SteveRMann/Halloween-2023/dfPlayer/DFPlayer-Wemos-ESPHome.jpg

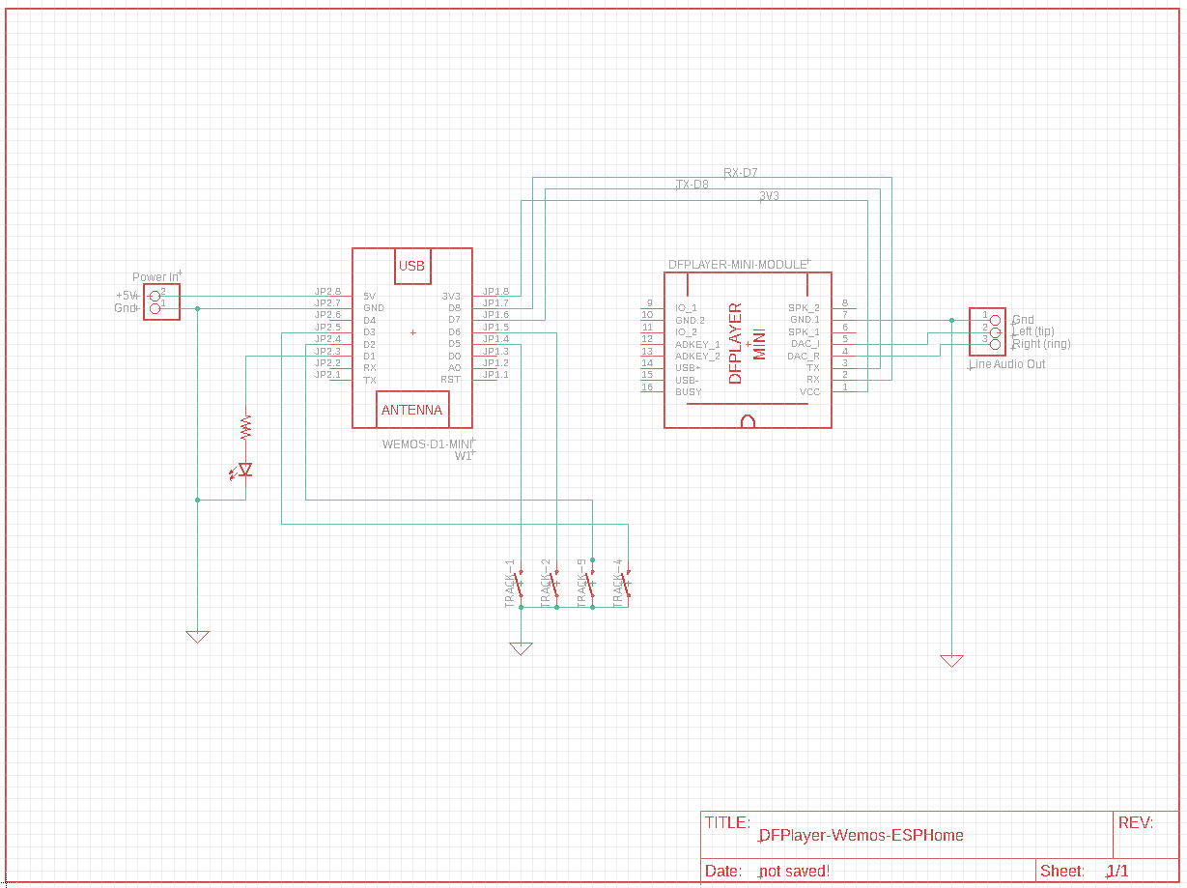
dfPlayer/DFPlayer-Wemos-ESPHome.jpg
