SteveRMann/Halloween-2023/dfPlayer/DFPlayer-Wemos-GPIO control.jpg

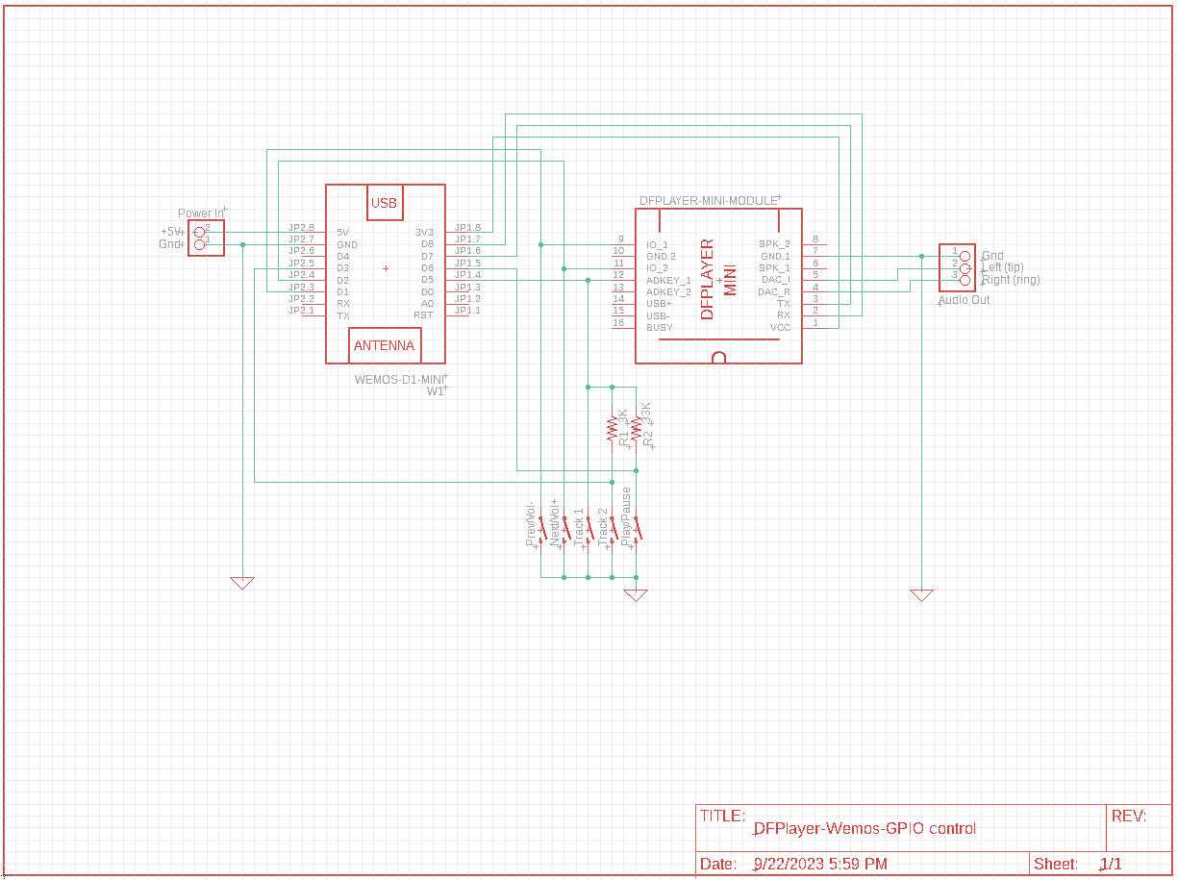
dfPlayer/DFPlayer-Wemos-GPIO control.jpg
