SteveRMann/Halloween-2023/dfPlayer/wemos_shield.png

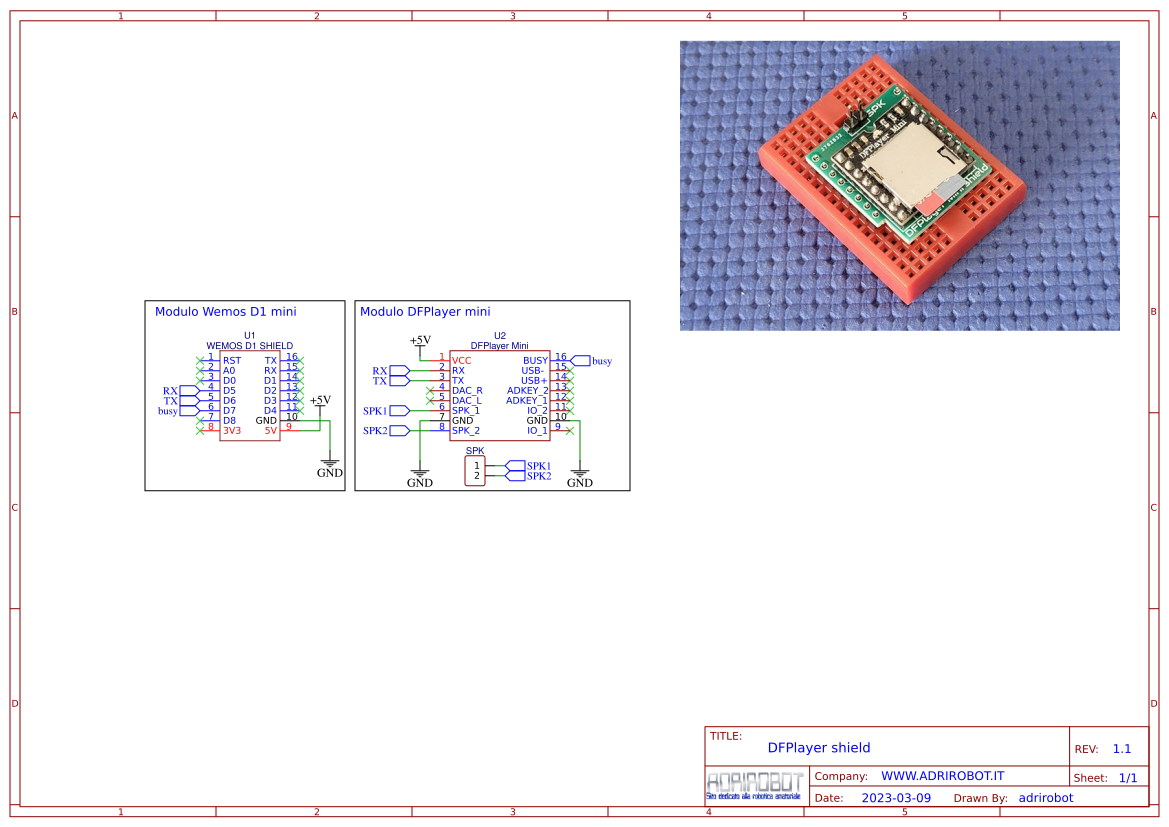
dfPlayer/wemos_shield.png
