SteveRMann/Halloween-2023/dfPlayer/DFPlayer-Wemos-ESPHome.sch

## EAGLE design dfPlayer/DFPlayer-Wemos-ESPHome.sch (2024-05-11)

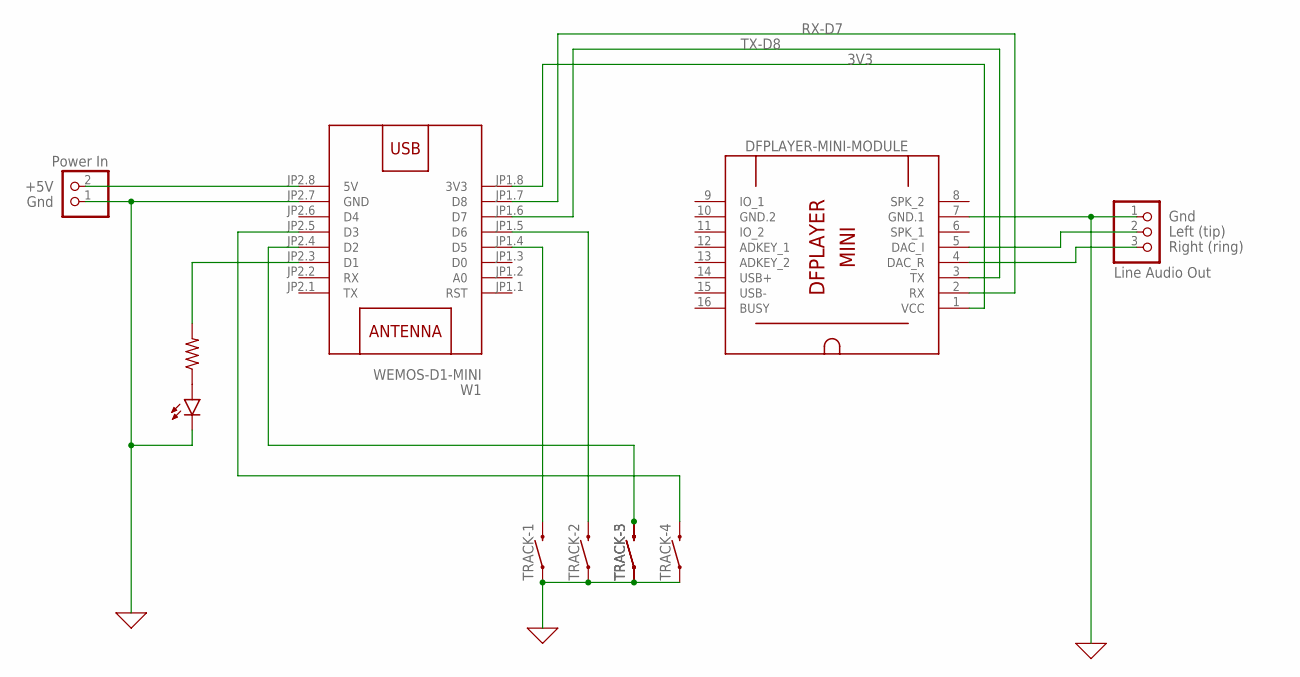
[picture p10: schematic DFPlayer-Wemos-ESPHome.sch]

Parts:
D1: WP7113SGD; RADIAL_5MM
JP2: Line Audio Out; 1X03
JP3: Power In; 1X02
R1: R-US_0204/5; 0204/5
TRACK-1, TRACK-2, TRACK-3, TRACK-4, TRACK-5: MOMENTARY-SWITCH-SPST-PTH-6.0MM; TACTILE_SWITCH_PTH_6.0MM
U$1: DFPLAYER-MINI-MODULE
W1: WEMOS-D1-MINI

Connections:
0: D1.C, JP2.1, JP3.1, TRACK-1.1, TRACK-2.1, TRACK-3.1, TRACK-4.1, TRACK-5.1, U$1.7 (GND.1), W1.JP2.7 (GND)
3V3: U$1.1 (VCC), W1.JP1.8 (3V3)
unnamed: D1.A, R1.1
unnamed: R1.2, W1.JP2.3 (D1)
unnamed: JP3.2, W1.JP2.8 (5V)
unnamed: TRACK-2.3 (2), W1.JP1.5 (D6)
unnamed: TRACK-3.3 (2), TRACK-5.3 (2), W1.JP2.4 (D2)
unnamed: JP2.2, U$1.5 (DAC_I)
unnamed: TRACK-1.3 (2), W1.JP1.4 (D5)
unnamed: JP2.3, U$1.4 (DAC_R)
unnamed: TRACK-4.3 (2), W1.JP2.5 (D3)
RX-D7: U$1.2 (RX), W1.JP1.7 (D8)
TX-D8: U$1.3 (TX), W1.JP1.6 (D7)

Notes on the sheet:
Gnd
Left (tip)
Right (ring)
+5V
